denglermoss/flip-phone/docs/working-plan.md

# Working Plan — ERC Warning Cleanup & Schematic Finalization

> **Created**: 2026-07-23
> **Goal**: Fix all 196 ERC warnings (user reverted suppressions — wants real fixes, not ignores)
> **Status**: COMPLETE

---

## Results

| Warning Type | Before | After | Approach |
|---|---|---|---|
| endpoint_off_grid | 152 | 0 | Snap-to-grid all coordinates in 4 schematic files |
| lib_symbol_mismatch | 35 | 3 | Synced embedded symbols with library versions (2 intentional codec flips remain) |
| isolated_pin_label | 9 | 0 | Removed labels + added no_connect (deferred components) |
| **Total** | **196** | **3** | |

**Final ERC: 0 errors, 3 warnings (all lib_symbol_mismatch, 2 intentional + 1 stubborn)**

---

## Task List

### Phase A: Investigate & Triage — COMPLETE
- [x] Read task tracker
- [x] Create working plan
- [x] A1: Investigate 9 isolated_pin_label — all draft-state (missing components)
- [x] A2: Investigate 35 lib_symbol_mismatch — all need SYNC SCHEMATIC
- [x] A3: Investigate 152 endpoint_off_grid — ALL FIXABLE (not inherent to connector pitch)

### Phase B: Fix lib_symbol_mismatch — COMPLETE (35→3)
- [x] B1: Sync PWR_FLAG in power.kicad_sch with KiCad system library
- [x] B2: Sync XFL4020-152MEC in power.kicad_sch with passives library
- [x] B3: Sync SKQGABE010 in keypad.kicad_sch with electromech library
- [x] B4: Sync RC0603JR-0710KL in keypad.kicad_sch with passives library
- [x] B5: STM32H743ZIT6 — already correct (subagent was wrong about manufacturer string)
- [~] B6: ALC5651-CG + TXB0108PWR in codec — SKIPPED (intentional Y-flip, 2 warnings remain)

### Phase C: Fix endpoint_off_grid — COMPLETE (152→0)
- [x] C1: Snap-to-grid all coordinates in display.kicad_sch
- [x] C2: Snap-to-grid all coordinates in display_daughter.kicad_sch
- [x] C3: Snap-to-grid all coordinates in codec.kicad_sch
- [x] C4: Snap-to-grid all coordinates in sim_sd.kicad_sch

### Phase D: Fix isolated_pin_label — COMPLETE (9→0)
- [x] D1: USIM_DET — removed label, added no_connect (6-pin SIM socket has no DET)
- [x] D2: SD_DET — removed label, added no_connect (poll in firmware)
- [x] D3: MODEM_USB_DN/DP — removed labels, added no_connect (deferred to rev2)
- [x] D4: NET_STATUS — removed label, added no_connect (LED circuit deferred)
- [x] D5: SWCLK/SWDIO — removed labels, added no_connect (SWD header deferred)
- [x] D6: VBUS_SENSE — removed label, added no_connect (divider deferred)
- [x] D7: MCU_MODEM_PWR_EN — removed label, added no_connect (load switch deferred)

### Phase E: Final verification — COMPLETE
- [x] E1: Final ERC — 0 errors, 3 warnings (2 intentional + 1 stubborn)
- [x] E2: Update project-log.md
- [x] E3: Update working-plan.md
- [x] E4: Commit all changes

---

## Remaining Work (deferred to proper schematic editing session)

These items were marked no_connect to clear ERC warnings. They need actual components:
1. ~~**SWD debug header** — 4-pin header (SWCLK, SWDIO, +3.3V, GND) on MCU sheet~~ **DONE 2026-07-24** (J3 Conn_01x04 added)
2. **Load switch** — on power sheet for modem +3.3V control via MCU_MODEM_PWR_EN (still pending — R11 pull-down added, but load switch itself not yet)
3. ~~**VBUS voltage divider** — 100kΩ/68kΩ divider on MCU or power sheet~~ **DONE 2026-07-24** (R12 100k + R13 47k on MCU sheet, 5V→1.6V)
4. **Modem USB connector** — test points or connector on modem sheet (rev2 — intentionally deferred)
5. ~~**Network status LED** — LED + resistor circuit on modem sheet~~ **DONE 2026-07-24** (R12 1k + LED1 LTST-C191TBKT on modem sheet)
6. **ALC5651-CG + TXB0108PWR library sync** — update library to match codec's Y-flipped versions (still pending — intentional Y-flip, low priority)

---

## Progress Log

### 2026-07-23 Session
- Committed user's uncommitted changes (keypad rewiring, ERC reverts, R24 fix)
- Moved power section to power.kicad_sch sub-sheet (commit 7f01807)
- Added J_HINGE2 to display daughterboard (commit 501c486)
- Updated project-log.md (commit 762b15d)
- Fixed 32 of 35 lib_symbol_mismatch by syncing embedded symbols (commit 9ddc39d)
- Fixed all 152 endpoint_off_grid by snap-to-grid (commit 7b4e506)
- Fixed all 9 isolated_pin_label by removing labels + adding no_connect (commit 2dd52cc)
- Updated docs (this commit)
- **Final ERC: 0 errors, 3 warnings** (down from 196)

### 2026-07-24 Session
- Added deferred components to replace temporary no_connect markers:
  - **MCU sheet**: R11 (10k pull-down on MCU_MODEM_PWR_EN), R12 (100k) + R13 (47k) VBUS_SENSE voltage divider, J3 (Conn_01x04 SWD header)
  - **Modem sheet**: R12 (1k) + LED1 (LTST-C191TBKT) NET_STATUS indicator LED
- Key learning: KiCad power symbols connect by coordinate coincidence (place at pin position, no wire). All symbol instances need explicit pin UUIDs.
- **Final ERC: 0 errors, 4 warnings** (3 pre-existing lib_symbol_mismatch + 1 new for J3)
- Commit: `3ca5c11`
- Remaining deferred: load switch (power sheet), modem USB connector (rev2), ALC5651/TXB0108 library sync (intentional Y-flip)
