denglermoss/flip-phone/docs/ref/constraints.md

---
status: reference
updated: 2026-08-27
---
# Constraints

## Technical Constraints

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

### PCB Design
- Single-board design (candybar form factor, LOCKED 2026-08-16). No multi-board split — display mounts directly via ZIF connector. Flip/clamshell deferred to v2.
- RF trace design for cellular antenna requires impedance control (50Ω) and possibly FCC layout guidelines.
- Antenna: can use off-the-shelf cellular antenna component or PCB trace antenna (latter is harder).
- **Board size target (MPCIe variant, 2026-07-22, updated 2026-08-16)**: **Single board < 2×3 inches (~50×76mm, ~3800mm²) as a target — but candybar form factor allows a larger board if needed.** First-pass estimate was ~100×65mm (conservative, most parts on top); revised to ~55×78mm with aggressive 2-sided placement (MCU + most ICs on bottom under keypad zone or under display; MPCIe + keypad stacked on top sharing the 54mm width). Candybar benefit: components can go under the display area, no hinge placement constraint. Deferred to KiCad layout for real numbers — not recalculated yet. MPCIe modem (54×32mm keepout) is the largest single block and sets the ~54mm minimum dimension. ~~Display daughterboard ~55×42mm~~ **DROPPED 2026-08-16** (candybar — no daughterboard). See project-log.md 2026-07-22 Board Size Estimate + 2026-08-16 Form Factor Pivot.
- **Cellular module assembly (LGA reality)**: All candidate LTE modules (SIM7600, EG25-G, EG912U-GL, LARA-R6401) are LGA — none are hand-solderable with an iron. No LTE/VoLTE module exists in a hand-friendly package. Realistic path: JLCPCB assembly for the modem section (~$57–72: module + $3 extended fee + ~$24 fixture + solder joints), hand-solder the rest. Alternative: M.2 socket variant (module plugs in, no reflow) at cost of larger footprint. **SIM7600NA-H (C5380303) is a JLC pre-order part** — 0 in stock, JLC sources it from SIMCom on demand ~~($31.42, lead time ≤18 days auto-proceed / >18 days email confirmation)~~ **JLC price corrected 2026-07-22: $59.00/ea, 8-day lead time**. Stored in your private JLC library until PCBA order. **SIM7600G-H (C5355477, 39 in stock, $46.95) shares the identical 119-pin LCC+LGA package** — usable as a footprint fallback if NA-H library data is incomplete (do NOT buy G-H for the board: it lacks B71). SA-H and E-H are 87-pin LCC (different package) and lack B71 — disqualified. See NFR-3 update in requirements.md and project-log.md 2026-07-19 SIM7600 Variant Selection.
- **MPCIe form factor (primary 2026-07-22, PCM confirmed 2026-07-22)**: SIM7600NA-H-PCIE (S2-109KS-Z30G9) from Techship ~$50/ea — Mini PCIe socketed card. Same B71/B66/VoLTE/GNSS/PCM specs as the LGA NA-H. **PCM CONFIRMED** from SIM7600 Series PCIE Hardware Design V1.03 §2.2 (p14) and §3.10.1 (p29): pins 45 (PCM_CLK), 47 (PCM_OUT), 49 (PCM_IN), 51 (PCM_SYNC) — master mode, short sync, 16-bit, 2048kHz, 1.8V. Exact match to ALC5651 PCM Mode A. PCIE variant = no onboard codec = PCM active; PCIEA variant = onboard NAU8810 = PCM NC (analog audio instead). Part S2-109KS-Z30G9 ends in PCIE (not PCIEA). **All MPCIe socket options are SMD** (0.8mm pitch, right-angle, surface mount — NOT through-hole as previously stated). Socket reflows with the rest of the board — no iron work needed. Socket options: Amphenol G633A0520022U (LCSC C357792, 1589 stock, ~5mm height), SOFNG PCIE-52P40H (LCSC C444926, 3039 stock, 4mm height), Hanbo PCI-E-H52-52P (LCSC C3039346), **JLC basic C9900027618** (5.2mm height, no extended fee if going JLC PCBA). Dimensions: 50.8×31×5.35mm card (vs LGA 30×30×1.5mm — adds ~21mm length, ~4mm height). **Additional findings from V1.03 manual**: (1) SIM socket NOT onboard (§3.7 says "contact local sales" — Techship spec lists it as optional `o`, stock card does NOT have it; both variants need PCB SIM socket wired to USIM pins); (2) UART is 1.8V (§3.8, same as bare LGA — level shifter needed either way); (3) Pin mapping differs from LGA: PERST# (pin 22, reset), WAKE# (pin 1, wake host), W_DISABLE# (pin 20, RF disable), LED_WWAN# (pin 42, network status) — **no PWRKEY pin** (TBD how MPCIe module powers on/off); (4) I2C at 1.8V (§3.9, pulled up in-module); (5) USB 2.0 HS on pins 36/38 (same as LGA, VBUS internal to VBAT). **Approach: MPCIe is the primary form factor for the schematic + PCB layout. LGA (bare module) is the fallback — pivot only if MPCIe proves difficult during layout.** See project-log.md 2026-07-22 Schematic Approach + MPCIe Primary.
- **DIY assembly approach (under evaluation 2026-07-22)**: User considering full DIY assembly (no JLC PCBA) to save cost and as a learning goal. Only 1 board needed (no MOQ 2 without JLC PCBA). Plan: 1 modem + 2-3 board qty of all other parts (spares for DIY mistakes). Tools needed: reflow oven (T-962 ~$150) + preheater ($50-100) + stencil ($20-40, with modem area cut out if LGA) + solder paste ($15-30) + USB microscope ($30-50) + hot-air station ($50-100). 2-sided board: top (heavy: modem/MCU/codec/connectors) + bottom (light: ~20 keypad switches + passives). DIY sequence: stencil+populate+reflow bottom → flip → stencil+populate+reflow top. With MPCIe as the primary form factor, the modem socket is SMD (reflows with the rest of the board — no separate iron step) — remaining hard parts: ALC5651 QFN-40, TPS63021 VSON-14, FPC connectors 0.5mm pitch. See project-log.md 2026-07-22 assembly evaluation.
- **ESD protection (required for external connectors)**: All external-facing data lines need ESD protection diodes placed close to the connector:
  - **USB-C D+/D-**: USBLC6-2SC6 (bidirectional, SOT-23-6, ~$0.50) — protects MCU USB OTG_FS.
  - **SIM + microSD data lines**: ESDA6V1-5SC6 (5-line array, ~$0.50) — protects modem SIM interface and MCU SDMMC.
  - These are small, cheap, and standard practice for any device with external connectors. Omitting them risks ESD damage during handling.
- **Modem USB HS port (rev1 hard requirement, updated 2026-08-27)**: Route the SIM7600's USB 2.0 HS port (D+/D-) to the **USB2512 hub downstream port 1** on rev1. The hub presents both the modem (RNDIS/ECM for LTE tethering at HS 480 Mbps) and the MCU (MSC/CDC ACM at FS 12 Mbps) to an external USB host over a **single USB-C port** — no second physical connector. Ecosystem is a hard rev1 requirement. The MCU's USB OTG_FS goes to hub downstream 2. See project-log.md 2026-08-27 USB Hub on Rev1.
- **GNSS antenna (rev1 decision, 2026-07-19)**: Include a **U.FL footprint** for the GNSS antenna on rev1. SIM7600 has built-in GNSS (validated 2026-07-12 on HAT — valid fix in ~60s cold start, works while registered on network). U.FL is a tiny SMD coaxial connector (~2mm) that connects the PCB to an off-board antenna via a short pigtail — standard for cellular/GPS modules. Low cost (~$0.50 connector + ~$2–5 antenna). User wants this board to potentially be the final version — deferring would mean a respin to add it later.
- **SIM + microSD connector strategy (rev1 decision, 2026-07-19)**: **Deferred to sourcing.** Both combo SIM+microSD sockets (saves board space, common in phones) and separate sockets (easier to source, more placement flexibility, larger footprint) are viable. Decision will be made at BOM finalization based on reliable availability from DigiKey/Mouser/LCSC. If a combo socket is reliably in stock at a reasonable price, use it; otherwise use separate sockets. Both blocks appear in the block diagram either way.
- **USB-C connector type (formally locked 2026-07-19)**: 16-pin USB-C (USB 2.0) for the main MCU USB connector. USB FS/HS only needs D+/D- — 24-pin USB 3.x is unnecessary. Micro-USB is obsolete and not considered.

### Power
- Cellular modules can draw 2A+ peaks during transmission — battery and power management must handle this.
- **Power architecture (resolved 2026-06-28)**:
  - **+BATT (modem)**: Powered **directly from the LiPo** (3.4–4.3V matches the LiPo operating range 3.4–4.2V). No buck regulator needed — the previous "dedicated high-current buck regulator" was incorrect. The key requirement is a **separate power net** from the MCU's 3.3V rail (so modem 2A bursts don't droop the MCU rail), with substantial bulk capacitance at the module VBAT pins.
  - **3.3V system rail**: Powered from the LiPo via a **buck-boost regulator** (**TPS63021DSJR**, 3.3V fixed, 4A switches / ~3A output, LCSC C202140 — LOCKED 2026-07-19). A buck-only regulator is insufficient — the LiPo drops below 3.3V at ~40% charge, and the MCU/display/SD card need a stable 3.3V. Powers: MCU, display, SD card, codec I2S side, level shifter, fuel gauge. *(Note: docs previously referenced "TPS630201" — that was a phantom part number TI never manufactured. Corrected to TPS63021DSJR 2026-07-19. See project-log.md.)*
  - **1.8V codec rail**: Powered from the 3.3V rail via an LDO (TPS7A0218, 200mA). Low current (~10–20mA for ALC5651).
  - **Charging**: USB 5V → MCP73831 charger IC → LiPo. The charger tops up the battery; the battery handles all load currents (including 2A modem peaks). The MCP73831 (500mA) does NOT need to handle modem peaks — the battery does. For production: consider a power-path charger (e.g., BQ25895, 5A) that can supply system load + charge simultaneously; for prototype, MCP73831 is sufficient.
- **+BATT rail stability (CRITICAL)**: The SIM7600 requires VBAT to remain within tolerance (typically ±100–200 mV) **during 2A transmit bursts**. If the rail droops, the module resets mid-call. This demands:
  - ~~A dedicated high-current buck regulator for the module VBAT rail (not shared with MCU rails)~~ **RESOLVED 2026-06-28**: Direct from LiPo — no regulator. The "dedicated rail" requirement is satisfied by a separate power net (+BATT net ≠ +3.3V MCU net), not a separate regulator.
  - Substantial low-ESR bulk capacitance near the module VBAT pins (typically 100–470 µF ceramic + tantalum)
  - Short, wide PDN traces to VBAT pins
  - This is a schematic review checklist item and a PCB layout constraint.
- Battery: single-cell LiPo (3.7V nominal, 3.0–4.2V range). 1200mAh candidate gives ~45h standby.
- Charging: USB-C with a battery charger IC (MCP73831 candidate). **USB-C strongly recommended** for any new design (micro-USB is obsolete).
- **Battery fuel gauge (required for FR-4.2)**: The phone must monitor and display battery level. Selected approach: **MAX17048** I2C fuel gauge (ModelGauge, coulomb counting + voltage, ~$2.50). Shares I2C bus with ALC5651. Provides state-of-charge (%) — more accurate than ADC voltage-only (which can't track coulomb count during 2A modem bursts). Alternative: ADC voltage-only (cheaper, less accurate — no coulomb counting, ~10% error vs ~1% for fuel gauge IC).
- Battery capacity vs form factor tradeoff — candybar / single-board form factor locked 2026-08-16. Final enclosure volume TBD (Phase 7 mechanical design).
- **Standby current note (verified 2026-06-28 from datasheets)**: The SIM7600's LTE idle/DRX current is **17.5 mA** (the state where the module CAN receive incoming calls). The previously cited "3 mA" figure is deep-sleep, where the module cannot receive calls. To satisfy FR-1.2 (receive calls) and FR-4.3 (idle low-power with modem standby), the module must remain in LTE idle/DRX mode. The 24h standby target (FR-4.4) requires ~420 mAh minimum (17.5 mA × 24h) — achievable with an 800+ mAh battery with comfortable margin. All modules support `AT+CEDRXS` for eDRX cycle tuning (longer cycle = lower current, higher call setup latency). The modem dominates standby power; MCU sleep (~20 µA) is negligible. See research-notes.md modem revisit findings for comparison across modules.

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

### Form Factor
- **Candybar / single-board form factor LOCKED 2026-08-16.** One PCB with all components — display mounts directly via ZIF connector (J7, 12-pin 0.5mm). No hinge flex, no daughterboard, no outer display. See project-log.md 2026-08-16 Form Factor Pivot. (Supersedes 2026-07-19 flip/clamshell decision, which is deferred to v2.)
- **Board architecture** (single board):
  - MCU, modem, codec, keypad, battery, power (charger + buck-boost + LDO + fuel gauge), USB-C, SIM, SD, cellular/GNSS antennas, microphone, loudspeaker, level shifter, ESD protection, crystals, passives, **main display panel** (HS20HS072RX, 2.0" ST7789T3 via J7 ZIF), **earpiece speaker**, **backlight FET + resistors**.
  - Display panel is 3.3V-only TFT (no boost converter). **Display panel purchased separately from PCB (LCSC) and assembled by user** — ZIF connector is JLC-assembled on PCB; panel plugs in post-assembly. This decouples display sourcing from PCB fab.
  - ~~Outer display (ER-TFT1.14-2)~~ **DROPPED 2026-08-16** — only makes sense on a flip lid.
  - ~~Hinge flex cable~~ **DROPPED 2026-08-16** — no hinge, no daughterboard.
- **Camera**: Out of scope for rev1. Will go on the single board when added — DCMI parallel bus (11 pins + 1 power) stays on the board, no flex signals. The 41 spare GPIO on LQFP-144 already accounts for DCMI in the GPIO budget (now 43 spare with PG9/PG10 freed from outer display).
- ~~**Hinge mechanism**~~ **DROPPED 2026-08-16** (candybar — no hinge). ~~Deferred to Phase 7. Options: salvage from existing flip phone, custom 3D printed, off-the-shelf metal hinge, or CNC machined.~~
- **Enclosure design**: Deferred to Phase 7. 3D model in CAD, fit-check with single PCB. Single-shell enclosure (no hinge, no two-piece lid/base).

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

### USB / Ecosystem Interconnect
- **MCU USB: OTG_FS only (12 Mbps, built-in PHY).** Sufficient for firmware updates, file/MSC transfer, and CDC ACM debug. ~~USB HS via external ULPI transceiver (USB3300) is a board-level upgrade path preserved by LQFP-144.~~ **DROPPED 2026-06-28** — see below.
- **Ecosystem tethering uses the SIM7600's own USB 2.0 HS port (480 Mbps), not the MCU.** The modem presents itself as a USB network adapter via RNDIS (`AT+CUSBPIDSWITCH=9011,1,1`) or ECM (`=9018,1,1`), simultaneously exposing AT/ttyUSB serial ports (composite device). This bypasses the MCU entirely for tethering — no MCU USB bottleneck, no USB3300 ULPI transceiver, no Zephyr USB HS stack, no 12 ULPI GPIO pins. The MCU controls the modem via UART (CMUX+PPP); the modem's USB is dedicated to tethering. See project-log.md 2026-06-28 USB HS/ULPI Revisit and research-notes.md "USB HS / ULPI Revisit" section.
- **Do NOT populate USB3300.** The ULPI footprint is wasted board space under the modem-direct tethering architecture. The 12 ULPI pins on LQFP-144 are freed for other future use.
- **PCB routing (rev1, ecosystem hard requirement — 2026-08-27)**: USB-C D+/D- → USBLC6-2 ESD → USB2512 hub upstream. Hub downstream 1 → modem USB (RNDIS/ECM, HS). Hub downstream 2 → MCU USB OTG_FS (MSC/CDC ACM, FS). Single USB-C port for both LTE tethering and MCU file/debug access. See project-log.md 2026-08-27 USB Hub on Rev1.
- **Hub requirements**: USB2512 (2-port HS hub, QFN-24) + 24MHz crystal + decoupling caps + +3.3V power + reset (RC or 1 MCU GPIO) + VBUS_DET (tap existing VBUS net via divider). Hub is powered whenever phone is on (+3.3V).
- **Pre-PCB verification**: Validate `AT+CUSBPIDSWITCH=9018,1,1` (ECM) and `=9011,1,1` (RNDIS) on the Waveshare NA-H HAT connected to a Linux host (the HAT exposes the modem USB). Confirm whether the modem can run PPP-over-UART (MCU data) simultaneously with RNDIS-over-USB (car module data) on two PDP contexts.

## Budget Constraints

- **Target**: Keep relatively low; flexible but avoid unnecessary spending.
- **Major cost categories**:
  - Cellular module: $10-40 depending on generation (2G cheapest, LTE more expensive)
  - Microcontroller: $3-15
  - Display: $3-15
  - PCB fabrication: $5-50 per board (JLCPCB/PCBWay, price scales with complexity)
  - PCB assembly (if not hand-soldering): $20-80 per board
  - Battery: $5-15
  - Miscellaneous components (connectors, switches, audio, power ICs): $20-50
  - ~~Flex cable / FPC: $5-20 (only if multi-board form factor chosen later)~~ **N/A 2026-08-16** (candybar — no flex cable)
  - Enclosure materials: $10-30 (3D printing)
- **Prototype BOM target**: < $150/unit
- **Total project budget** (including multiple iterations, tools, mistakes): $200-500 realistic

## Regulatory Constraints

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

## Timeline Constraints

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

## Skill / Tooling Constraints

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

## AI-Assisted KiCad Editing Constraints (set up 2026-07-22)

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
