denglermoss/flip-phone/docs/ref/research-notes.md

---
status: reference
updated: 2026-08-27
---
# Research Notes

## Cellular Communication Primer

### How Phone Calls Work (Simplified)

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

### What a Cellular Module Does

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

### AT Commands — The Interface

Your MCU sends text commands to the module over UART. Examples:
```
AT              -> Module responds "OK" (basic check)
ATD+1234567890; -> Dial a number
ATA             -> Answer incoming call
ATH             -> Hang up
AT+CSQ          -> Query signal quality
AT+CREG?        -> Query network registration status
AT+CMGS="..."   -> Send SMS
```

The module sends **unsolicited result codes (URCs)** for events:
```
RING            -> Incoming call
+CMGS: <n>      -> SMS sent successfully
+CREG: 1        -> Registered on network
```

Your firmware must parse these asynchronously — the module can send URCs at any time.

### Network Generation Comparison

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

### Module Candidates (Initial List)

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

### Architecture Decision (Module Category)

Four architectures were evaluated, not just module models:

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

### SIM Cards

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

## MCU Candidates

### Initial List (Historical)

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

### Final Selection Analysis

The "no 5+ features blocked" principle and concurrent processing load requirement drove the selection:

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

**Selected: STM32H743 (LQFP-144, STM32H743ZI)**

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

### Package Selection

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

#### USB HS / ULPI Clarification

The STM32H743 has two separate USB OTG controllers on the silicon:

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

#### LQFP-144 vs LQFP-176 Detailed Tradeoff Analysis

**1. GPIO count: 106 vs 140 (34 extra pins on 176)**

Worst-case GPIO budget for the phone (all peripherals populated):

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

Future additions:

| Future peripheral | Pins | Notes |
|---|---|---|
| ~~USB OTG_HS (ULPI)~~ | ~~12~~ | ~~External USB3300 transceiver, for ecosystem tethering~~ **DROPPED 2026-06-28** — modem-direct USB tethering replaces MCU USB HS (see USB HS/ULPI Revisit). 12 pins freed. |
| Modem USB (D+/D-) | 2 | SIM7600 USB 2.0 HS port routed to USB2512 hub downstream 1 (rev1 hard requirement — 2026-08-27); hub presents modem + MCU over single USB-C |
| External BT module | 4 | UART + power/control |
| **Subtotal** | **6** | ~~16~~ (was 16 with ULPI; now 6 with modem USB + BT) |

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

**2. Camera bit depth: 8-bit (144) vs 14-bit (176)**

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

**3. FMC (external memory bus): 16-bit (144) vs 32-bit (176)**

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

Main use case is display framebuffers. The H743 has 1MB internal SRAM. Display framebuffer sizes:

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

#### Package Selection Conclusion

Every factor favors the 144 or is a wash:

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

### Bluetooth Strategy

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

### Power Note

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

## Camera & Video Recording Analysis

> **RESOLVED 2026-08-17**: Camera module selected — **OV5640** (5MP, auto-focus, 8-bit DVP). See `docs/ref/project-log.md` 2026-08-17. The analysis below remains valid as reference for DCMI bandwidth, JPEG paths, and video recording feasibility. Key findings confirmed during selection:
> - OV5640 has on-chip JPEG (same as OV2640) — the JPEG bandwidth/memory analysis below applies.
> - STM32H743 hardware JPEG codec confirmed in Zephyr (`st,stm32-jpeg` driver, PR #110278) — Path 2 (HW encode/decode) is available as a fallback/complement to sensor-side JPEG.
> - Zephyr OV5640 DVP driver (merged Feb 2025) currently exposes only 480×272 RGB565 — needs extension for VGA+/JPEG/AF. This is firmware work, not a hardware restriction.
> - OV2640 Zephyr driver is more mature (JPEG at all resolutions, tested on H743 DCMI) but OV2640 is 2MP fixed-focus vs OV5640's 5MP auto-focus. Quality difference justified the firmware tradeoff.

### DCMI Hardware Limits (STM32H743)

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

### Video Resolution vs Frame Rate (8-bit DVP, RGB565/YCbCr422 = 2 bytes/pixel)

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

### Memory Constraint (the harder limit)

Where do video frames go? Internal SRAM is 1MB.

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

### JPEG Compression (the escape hatch)

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

### H7 Hardware JPEG Codec

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

### Practical Video Recording Summary

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

### Would 10/12/14-bit (LQFP-176) help with video?

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

**The 14-bit bus doesn't meaningfully improve video recording for this use case.**

## Display Options

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

### Options Evaluated

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

### Why ST7789V SPI TFT Was Selected

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

### Why Not LTDC Parallel RGB

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

### Why Not E-ink

E-ink is **disqualified** by the "no 5+ features blocked" principle on two independent grounds:

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

### Why Not Color OLED (SSD1351)

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

### Selected Panel

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

### Pre-PCB Verification Items

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

## Open Research Questions

- [x] **RESOLVED (2026-07-12)**: Does VoLTE "just work" via AT commands, or is there significant configuration? — **Yes, VoLTE works.** `AT+voltesetting=1` on LE20B02 firmware returned OK. IMS PDP context (cid=2) auto-created by the network. `AT+CNSMOD: 0,8` confirms LTE mode (not CSFB). Test call connected successfully on Mint/T-Mobile. No firmware update needed — LE20B02 supports VoLTE despite being older than the documented LE20B04/05 versions. The IMS PDP context quirk (cid=2 conflict with cid=1 data) is specific to `AT+NETOPEN` and does not affect this project (uses CMUX+PPP). Validated empirically with Waveshare NA-H HAT + Mint SIM.
- [x] **RESOLVED**: Can we use the module's built-in audio path or do we need an external codec? — SIM7600 (LCC package) exposes PCM digital audio only, no analog pins. External codec required. **ALC5651 selected** (dual-port: PCM + I2S). See Codec Selection section. The EG912U-GL has analog audio but was rejected for the two-audio-path problem with music playback.
- [x] **RESOLVED (2026-07-12)**: Which carriers allow VoLTE on non-certified devices with prepaid SIMs? — **Mint/T-Mobile allows VoLTE on the SIM7600NA-H.** VoLTE call connected successfully with `AT+voltesetting=1` on a Mint Mobile SIM. The SIM7600NA-H's T-Mobile certification likely helps. No IMEI whitelisting issues encountered. AT&T/Verizon remain untested but are stricter — not needed since Mint works.
- [ ] What's the minimum antenna design for LTE? Can we use a small chip antenna or stamped antenna?
- [x] **RESOLVED (2026-06-28, second round)**: Can the SIM7600 maintain simultaneous VoLTE call + data tethering? — **Not a requirement.** Simultaneous VoLTE+data is a future ecosystem feature (tethering while on a call), not needed for MVP or daily driver. The PDP context conflict is confirmed in the `AT+NETOPEN` code path only; the project uses CMUX+PPP which bypasses it. CMUX+PPP is the standard pattern for simultaneous data + AT commands (SMS, calls) on the SIM7600, proven in Linux n_gsm, RT-Thread, and ESP-IDF. Whether data stays active *during* a live VoLTE call via PPP is unverified but likely (3GPP bearers should coexist). **Fallback: pause data during calls — acceptable for all current and planned use cases.** This is no longer a modem selection factor.
- [ ] Are there any open-source cell phone projects we can reference?
- [x] **RESOLVED (2026-07-12, partial)**: Does SIM7600 GNSS work standalone or only when module is registered on network? — **GNSS works while module is registered on the network.** `AT+CGPS=1` → `AT+CGPSINFO` returned a valid fix (42.35°N, -76.43°W, Ithaca NY area) in ~60 seconds from cold start. Whether GNSS works *without* network registration was not tested (modem was registered the whole time). For the ecosystem use case (car module uses phone GPS), the phone will always have network registration when in use, so this is sufficient. GNSS antenna must be connected.
- [x] **RESOLVED**: Which ESP32 variants have USB OTG? (ESP32-S2, ESP32-S3 have native USB; original ESP32 does not) — Moot; STM32H743 selected.
- [x] **RESOLVED (2026-06-28)**: Which display type should the phone use? — **ST7789V SPI color TFT, 2.0" 240×320, RGB565.** Five options evaluated: (1) SPI color TFT ST7789V — **SELECTED**; (2) SPI color OLED SSD1351 — rejected (actually HIGHER power than TFT at ~57–71mA, 3–5x cost at $15–24, 128×128 too low, not in Zephyr main tree); (3) E-ink — **DISQUALIFIED** (blocks three 5+ features: camera preview 6 at ~0.5–3fps refresh, photo capture 6 with spot-color only no blue/green, video 5; true color e-ink not available at 1.5–2.4"); (4) LTDC parallel RGB — rejected (20–28 GPIO, needs external SDRAM, overkill res); (5) SPI TFT ST7735 1.8" 128×160 — rejected (too low res). ST7789v driver (`display_st7789v.c`) is the most mature SPI display driver in Zephyr main tree with native LVGL support. 6 GPIO pins, 150KB framebuffer fits internal 1MB SRAM (no external SDRAM), ~$5–8, color-capable, lower power than the OLED alternative. Pre-PCB: verify ST7789v driver on STM32H7 + target Zephyr version (MIPI DBI API conversion had teething issues). See Display Options section and project-log.md 2026-06-28 Display Selection.
- [x] **RESOLVED (2026-06-28, updated 2026-07-19)**: Which codec best supports both PCM (voice from SIM7600) and I2S (music from MCU) inputs? — ~~MAX9880A selected~~ **SUPERSEDED 2026-07-19** — replaced by **Realtek ALC5651-CG** (LCSC C963633, QFN-40 5×5mm, JLC Extended — no consignment). Key findings: (1) All common codecs (WM8960, NAU8810, NAU8822, SGTL5000, TLV320AIC3204/3104, ES8316/8388) have only ONE digital audio input port — they cannot accept PCM and I2S simultaneously. The original "single codec unifies voice and music" claim was false for these parts. (2) Dual-port codecs are rare: MAX9880A (Maxim/ADI, TQFN-48) and ALC5651/ALC5640/ALC5642 (Realtek, QFN-40/48). (3) The SIM7600 outputs PCM only (fixed master mode, short-frame sync, 16-bit linear, 2048/4096kHz) — no I2S mode, not configurable. (4) With the ALC5651, the MCU is NOT in the voice audio path during calls (SIM7600→PCM→codec I2S-1→speaker directly), matching real smartphone architecture. (5) ALC5651 selected over MAX9880A because it's JLC-sourced (no Mouser consignment), has better specs (100dBA DAC vs 96dB, 94dBA ADC vs 82dB), smaller package (QFN-40 5×5mm vs TQFN-48 6×6mm), and ASRC per interface. (6) Fallback if ALC5651 is unavailable: MCU bridge (SAI1 PCM slave + SAI2 I2S master + single-port codec like NAU8822) — feasible but adds ~8-10ms latency and depends on Zephyr H7 SAI driver maturity. See Codec Selection / Audio Path Architecture section and project-log.md 2026-07-19 Codec Swap.
- [x] **RESOLVED (2026-06-28, updated 2026-08-27)**: Is Zephyr's STM32H7 USB OTG_HS + ULPI support mature enough for the ecosystem tethering path? — **Yes, it is viable (mainline since Dec 2022, PR #52772; bugs #61464/#75119 fixed; works on STM32H747I-DISCO), BUT it is no longer needed.** The SIM7600's own USB 2.0 HS port (480 Mbps) does tethering directly via RNDIS/ECM (`AT+CUSBPIDSWITCH`), bypassing the MCU entirely — a better architecture that eliminates the MCU USB bottleneck, the USB3300 ULPI transceiver, the Zephyr USB HS stack risk, and the 12 ULPI GPIO pins. **Decision: drop USB3300/ULPI; use MCU USB OTG_FS (12 Mbps) for MCU-originated USB (firmware, files, debug); route the modem's USB to the USB2512 hub (on rev1 as of 2026-08-27 — ecosystem is a hard rev1 requirement) for tethering.** The "USB HS via ULPI is a board-level upgrade path preserved by LQFP-144" claim is superseded. See "USB HS / ULPI Revisit" section and project-log.md 2026-06-28 USB HS/ULPI Revisit + 2026-08-27 USB Hub on Rev1.

## Component Checklist (BOM items not yet specified in docs)

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

| Component | Purpose | Notes |
|---|---|---|
| Nano-SIM socket | SIM card holder for SIM7600 | LGA/SMD, typically Molex 786470-3001 or similar |
| Battery fuel gauge IC | Battery level monitoring (FR-4.2) | I2C. **Selected: MAX17048** (ModelGauge, coulomb counting, ~$2.50). Shares I2C bus with ALC5651. See `docs/ref/bom.md` item 12 and `docs/ref/constraints.md` Power section. |
| 3.3V buck-boost regulator | MCU/system rail from LiPo | **Selected: TPS63021DSJR** (fixed 3.3V, 4A switches / ~3A output, VSON-14/DSJ, LCSC C202140, ~$3.50 — LOCKED 2026-07-19). LiPo 3.0–4.2V → 3.3V. *Correction: docs previously said "TPS630201" — phantom part number, corrected to TPS63021DSJR.* See `docs/ref/bom.md` item 10 and `docs/ref/constraints.md` Power section. |
| ESD protection diodes | USB-C, SIM, microSD data lines | **Selected: USBLC6-2SC6** (USB) + **ESDA6V1-5SC6** (SIM/SD), ~$1 total. See `docs/ref/bom.md` items 23-24 and `docs/ref/constraints.md` PCB Design section. |
| Modem PWRKEY/STATUS GPIO | Power-cycle SIM7600 from MCU | 2 GPIO pins (PWRKEY output + STATUS input). See `docs/ref/constraints.md` MCU section. |
| Display backlight driver | Raw panel LED backlight (FET + resistors) | N-FET + current-limiting resistors + PWM GPIO for parallel-LED panels. Verify panel config before PCB. See `docs/ref/constraints.md` Display section. |
| 32.768 kHz crystal | Not needed (NITZ selected) | Only if RTC crystal approach is later adopted. See constraints.md timekeeping section. |
| USB-C connector | Data + charging + ecosystem interconnect | USB-C recommended over micro-USB. Connector type still TBD in requirements.md. |
| Earpiece transducer | Call audio (held to ear) | Separate from loudspeaker. See constraints.md audio topology note. |
| Loudspeaker | Ringtones, speakerphone (rated 3) | Codec has separate speaker output. |
| Audio codec | PCM voice (from SIM7600) + I2S music (from MCU) | **Realtek ALC5651-CG selected** (QFN-40 5×5mm, ~$1.00, LCSC C963633). Dual I2S/PCM: I2S-1 = PCM, I2S-2 = I2S. 1.8V analog + 1.2V digital (internal LDO) + 3.3V MICVDD. See Codec Selection section. |
| Color TFT display | Phone UI, camera preview, photo viewer | **ST7789V selected** (2.0" 240×320, 4-wire SPI, RGB565, ~$5–8). 6 GPIO pins. 150KB framebuffer fits internal SRAM. IPS variant preferred. See Display Options section. |
| 1.8V LDO regulator | ALC5651 analog supply | From 3.3V rail. |
| I2S level shifter | 3.3V MCU → 1.8V ALC5651 I2S-2 | Unidirectional (SCK, FS, SD, MCLK). Voltage divider or TXB010x. |

## Modem Revisit Findings

### First Round (2026-06-28)

A revisit of the SIM7600 selection evaluated four concerns: standby power, B71 validation, simultaneous VoLTE+data, and LGA assembly. **Conclusion: stick with SIM7600, with two changes** (switch prototyping HAT to NA-H; make VoLTE+data the first HAT test). Full rationale in `docs/ref/project-log.md` (2026-06-28 Modem Revisit).

### Second Round (2026-06-28) — Full Re-evaluation

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

#### LARA-R6401 — DISQUALIFIED (911/E911 not supported)

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

Sources: u-blox LARA-R6401 datasheet (UBX-20048923); DigiKey stock verification.

#### Quectel EC25-AF — Strong alternative, but not worth switching

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

#### EG25-G — T-Mobile VoLTE issue clarified

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

#### SIM7600 PDP context conflict — RESOLVED (not a blocker)

**The conflict is real but confined to the `AT+NETOPEN` code path.** Detailed findings:

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

#### Simultaneous VoLTE+data — NOT a requirement

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

#### Final Modem Comparison Matrix

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

### 1. Standby Power / Idle-DRX Current (RESOLVED — lower concern than expected)

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

### 2. B71 Validation Gap (RESOLVED — NA-H HAT exists)

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

### 3. Simultaneous VoLTE + Data (REAL RISK — test first, affects future feature only)

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

**AT command test sequence (run on HAT — use PPP, not AT+NETOPEN):**
```
# Phase 1: VoLTE validation (no data)
AT+SIMCOMATI                               # Check firmware version (note LE20B04 vs LE20B05)
AT+voltesetting=1                          # Enable VoLTE
AT+cnv=/nv/item_files/modem/mmode/ue_usage_setting,1,01,1
AT+CGDCONT?                                # Check existing PDP contexts (cid=1 data, cid=2 IMS auto-created)
AT+CNSMOD?                                 # Verify registered on LTE (mode 8), not CSFB to 3G/2G
ATD<phone_number>;                         # Place VoLTE call
AT+CLCC                                    # Call status
AT+CNSMOD?                                 # Verify still on LTE during call (not CSFB)
ATH                                        # Hang up

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

# Phase 3: Simultaneous VoLTE + data (informational, not blocking)
# While PPP is active on channel 2:
ATD<phone_number>;                         # Place VoLTE call on channel 1
# Test if data still flows on PPP channel during call
# If data pauses: acceptable — resume after call ends
ATH                                        # Hang up
# If data resumes after call: simultaneous works (bonus)
# If data does not resume: reconnect PPP
```

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

### 4. LGA Assembly (WASH — all candidates are LGA)

Every LTE module in the candidate set is LGA — none are hand-solderable with an iron:

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

## Codec Selection / Audio Path Architecture

### The Problem

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

### Finding 1: SIM7600 Audio Interface (PCM only, fixed)

Source: SIM7600 Series Hardware Design Manual V1.03, §3.6 "PCM Interface."

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

### Finding 2: Codec Digital Audio Port Survey

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

### Finding 3: MCU Bridge Feasibility (Fallback Architecture)

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

**Selected codec: Realtek ALC5651-CG (QFN-40 5×5mm, ~$1.00).**

Architecture:
```
Voice path (calls):
  SIM7600 PCM_OUT/IN/SYNC/CLK → ALC5651 I2S-1 (PCM slave, Mode A short-sync)
  ALC5651 → earpiece/speaker (analog out — HPO_L/R or LOUTL/P + LOUTR/N)
  Mic → ALC5651 (IN1P/IN2P/IN2N analog in) → I2S-1 ADCDAT → SIM7600 PCM_IN
  [MCU NOT in voice audio path]

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

Simultaneous voice + music:
  ALC5651 mixes internally (ASRC per interface — independent sample rates OK)
```

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

### Prototyping Impact

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

### Component Checklist Update

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

## USB HS / ULPI Revisit (Zephyr STM32H7 OTG_HS + ULPI Maturity)

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

### Finding 1: Zephyr STM32H7 USB OTG_HS + ULPI IS in mainline and works

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

### Finding 2: The SIM7600's own USB port does tethering directly — a better architecture

This is the bigger finding and changes the architecture.

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

### Finding 3: What the MCU's USB actually needs to do (all FS-sufficient)

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

### Finding 4: Topology options for the ecosystem connector

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

**Recommendation: ~~Topology D for rev1 (minimal commitment), with Topology A (internal hub) as the planned ecosystem path.~~** **SUPERSEDED 2026-08-27**: Topology A (internal USB2512 hub) is now the rev1 choice — ecosystem is a hard rev1 requirement, not deferred. See project-log.md 2026-08-27 USB Hub on Rev1. ~~Tethering is rated 6 (strong want, not must-have) and is explicitly post-daily-driver scope. Rev1 should preserve the modem USB routing option (footprint/test points) without committing to a hub chip. When the ecosystem module becomes a real project, respin with the USB2514 hub (Topology A) for the clean single-cable simultaneous LTE + file access.~~

### Recommendation Summary

1. **USB HS via ULPI on Zephyr/STM32H7 is viable** (mainline since Dec 2022, bugs fixed, works on the disco board) — but it is **no longer needed** for the tethering use case, because the SIM7600's own USB 2.0 HS port does tethering directly and better.
2. **Do NOT populate the USB3300 ULPI transceiver.** It is wasted board space given the modem-direct tethering architecture. The 12 ULPI pins are freed for other future use. The LQFP-144 package decision is retained (it was also chosen for its GPIO margin — 41 spare after dropping ULPI — camera, and overall peripheral fit — not ULPI alone).
3. **Use the MCU's USB OTG_FS (12 Mbps, built-in PHY)** for all MCU-originated USB needs (firmware, files, debug). FS is sufficient for all of them.
4. **Route the SIM7600's USB D+/D- to the USB2512 hub** on rev1 (ecosystem is a hard rev1 requirement as of 2026-08-27 — no longer deferred to a future respin). The internal USB 2.0 hub (Topology A) presents both the modem (RNDIS, 480 Mbps) and the MCU (MSC) to the host over a single USB-C cable — simultaneous LTE + file access, no MCU USB bottleneck, no ULPI. See project-log.md 2026-08-27 USB Hub on Rev1.
5. **Update the "USB mode" resolved question**: USB FS for the MCU is the committed path; USB HS via ULPI is dropped (not needed — modem handles tethering at HS directly). The phone remains a USB **device** in all ecosystem scenarios; the modem is also a USB device, and the internal hub (on rev1) presents both to the host.

### Pre-PCB / Prototype Verification Items (new)

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
